samk3ys/CoolSafe/Microcontroller/MorseLED/src/MorseLED.ino

/*
 * Project MorseLED
 * Description: blinks an LED in morse code of a message
 * Author: Sam Keys
 * Date: 11/14/2019
 */

#include "Particle.h"

#include "dct.h"

SYSTEM_MODE(MANUAL);    // avoid registration

//String morseMessage = "Hello, World!";
String morseMessage = "SOS";
//String morseMessage = "115";

const uint8_t LED = 11;
const uint timeUnit = 300;          // morse code time unit
const uint letterGap = timeUnit*2;  // gap btwn letters (3 = 2 + timeUnit)
const uint wordSpace = timeUnit*4;  // gap btwn words (7 = 4 + letterGap + timeUnit)

void setup() {
    pinMode(LED, OUTPUT); // pin to send morse code thru
}

void dit() {
    // light LED for 1 time unit
    digitalWrite(LED, HIGH);
    delay(timeUnit);
    digitalWrite(LED, LOW);
    delay(timeUnit);
}

void dah() {
    // light LED for 3 time units
    digitalWrite(LED, HIGH);
    delay(timeUnit*3);
    digitalWrite(LED, LOW);
    delay(timeUnit);
}

void loop() {
    morseMessage.toUpperCase();
    
    for (uint i = 0; i < morseMessage.length(); i++) {
        char current = morseMessage.charAt(i);

        switch (current)
        {
        case 'A': //.-
            dit(); dah();                       delay(letterGap);
            break;
        case 'B': //-...
            dah(); dit(); dit(); dit();         delay(letterGap);
            break;
        case 'C': //-.-.
            dah(); dit(); dah(); dit();         delay(letterGap);
            break;
        case 'D': //-..
            dah(); dit(); dit();                delay(letterGap);
            break;
        case 'E': //. 
            dit();                              delay(letterGap);
            break;
        case 'F': //..-.
            dit(); dit(); dah(); dit();         delay(letterGap);
            break;
        case 'G': //--.
            dah(); dah(); dit();                delay(letterGap);
            break;
        case 'H': //....
            dit(); dit(); dit(); dit();         delay(letterGap);
            break;
        case 'I': //..
            dit(); dit();                       delay(letterGap);
            break;
        case 'J': //.---
            dit(); dah(); dah(); dah();         delay(letterGap);
            break;
        case 'K': //-.-
            dah(); dit(); dah();                delay(letterGap);
            break;
        case 'L': //.-..
            dit(); dah(); dit(); dit();         delay(letterGap);
            break;
        case 'M': //--;
            dah(); dah();                       delay(letterGap);
            break;
        case 'N': //-.;
            dah(); dit();                       delay(letterGap);
            break;
        case 'O': //---
            dah(); dah(); dah();                delay(letterGap);
            break;
        case 'P': //.--.
            dit(); dah(); dah(); dit();         delay(letterGap);
            break;
        case 'Q': //--.-
            dah(); dah(); dit(); dah();         delay(letterGap);
            break;
        case 'R': //.-.
            dit(); dah(); dit();                delay(letterGap);
            break;
        case 'S': //...
            dit(); dit(); dit();                delay(letterGap);
            break;
        case 'T': //-; 
            dah();                              delay(letterGap);
            break;
        case 'U': //..-
            dit(); dit(); dah();                delay(letterGap);
            break;
        case 'V': //...-
            dit(); dit(); dit(); dah();         delay(letterGap);
            break;
        case 'W': //.--
            dit(); dah(); dah();                delay(letterGap);
            break;
        case 'X': //-..-
            dah(); dit(); dit(); dah();         delay(letterGap);
            break;
        case 'Y': //-.--
            dah(); dit(); dah(); dah();         delay(letterGap);
            break;
        case 'Z': //--..
            dah(); dah(); dit(); dit();         delay(letterGap);
            break;
        case '1': // .----
            dit(); dah(); dah(); dah(); dah();  delay(letterGap);
            break;
        case '2': // ..---
            dit(); dit(); dah(); dah(); dah();  delay(letterGap);
            break;
        case '3': // ...--
            dit(); dit(); dit(); dah(); dah();  delay(letterGap);
            break;
        case '4': // ....-
            dit(); dit(); dit(); dit(); dah();  delay(letterGap);
            break;
        case '5': // .....
            dit(); dit(); dit(); dit(); dit();  delay(letterGap);
            break;
        case '6': // -....
            dah(); dit(); dit(); dit(); dit();  delay(letterGap);
            break;
        case '7': // --...
            dah(); dah(); dit(); dit(); dit();  delay(letterGap);
            break;
        case '8': // ---..
            dah(); dah(); dah(); dit(); dit();  delay(letterGap);
            break;
        case '9': // ----.
            dah(); dah(); dah(); dah(); dit();  delay(letterGap);
            break;
        case '0': // -----
            dah(); dah(); dah(); dah(); dah();  delay(letterGap);
            break;
        case ' ': // gap
            delay(wordSpace);
            break;
        default:
            // don't blink
            break;
        }
    } // end for (done w/ morseMessage)

    delay(wordSpace); delay(wordSpace);

    //exit(0);
}
